danwallach/VoteBox-v2/java/src/test/java/edu/rice/starvote/MotorTest.java

package edu.rice.starvote;

import edu.rice.starvote.ballotbox.drivers.IMotor;
import edu.rice.starvote.ballotbox.drivers.PWMPython;
import edu.rice.starvote.ballotbox.drivers.PrinterMotor;
import org.junit.Test;

/**
 * Created by luej on 8/2/16.
 */
public class MotorTest {
    @Test
    public void test() throws Exception {
        IMotor motor = new PrinterMotor(22, 27, new PWMPython(17, 50, 0));
        motor.forward();
        Thread.sleep(1000);
        motor.forwardSlow();
        Thread.sleep(1000);
        motor.stop();
        Thread.sleep(1000);
        motor.reverse();
        Thread.sleep(1000);
        motor.reverseSlow();
        Thread.sleep(1000);
    }
}
